diyruz/freepad/Source/OSAL_FreePadApp.c

#include "OSAL.h"
#include "OSAL_Tasks.h"
#include "ZComDef.h"
#include "hal_drivers.h"

#include "APS.h"

#include "ZDApp.h"
#include "nwk.h"

#include "bdb_interface.h"
#ifdef FREEPAD_ENABLE_TL
#include "bdb_touchlink_initiator.h"
#include "stub_aps.h"
#include "tl_resetter.h"
#endif

#include "Debug.h"
#include "battery.h"
#include "commissioning.h"
#include "factory_reset.h"
#include "zcl_freepadapp.h"

const pTaskEventHandlerFn tasksArr[] = {macEventLoop,
                                        nwk_event_loop,
                                        Hal_ProcessEvent,
                                        APS_event_loop,
                                        ZDApp_event_loop,
                                        zcl_event_loop,
#ifdef FREEPAD_ENABLE_TL
                                        StubAPS_ProcessEvent,
                                        touchLinkInitiator_event_loop,
#endif
                                        bdb_event_loop,
                                        zclFreePadApp_event_loop,
                                        zclCommissioning_event_loop,
                                        zclFactoryResetter_loop,
                                        zclBattery_event_loop
#ifdef FREEPAD_ENABLE_TL
                                        ,
                                        zclTouchLinkRestter_event_loop
#endif
};

const uint8 tasksCnt = sizeof(tasksArr) / sizeof(tasksArr[0]);
uint16 *tasksEvents;

void osalInitTasks(void) {
    uint8 taskID = 0;
    DebugInit();

    tasksEvents = (uint16 *)osal_mem_alloc(sizeof(uint16) * tasksCnt);
    osal_memset(tasksEvents, 0, (sizeof(uint16) * tasksCnt));
    macTaskInit(taskID++);
    nwk_init(taskID++);
    Hal_Init(taskID++);
    APS_Init(taskID++);
    ZDApp_Init(taskID++);
    zcl_Init(taskID++);
#ifdef FREEPAD_ENABLE_TL
    StubAPS_Init(taskID++);
    touchLinkInitiator_Init(taskID++);
#endif
    bdb_Init(taskID++);
    zclFreePadApp_Init(taskID++);
    zclCommissioning_Init(taskID++);
    zclFactoryResetter_Init(taskID++);
    zclBattery_Init(taskID++);
#ifdef FREEPAD_ENABLE_TL
    zclTouchLinkRestter_Init(taskID++);
#endif
}

/*********************************************************************
*********************************************************************/
