diyruz/freepad/Source/preinclude.h

#define TC_LINKKEY_JOIN
#define NV_INIT
#define NV_RESTORE
// to make TL work, need patch this macroses in SDK
// #define TOUCHLINK_KEY_INDEX TOUCHLINK_KEY_INDEX_MASTER
// #define TOUCHLINK_INTERNAL_ENDPOINT 42

#define TP2_LEGACY_ZC
// patch sdk
// #define ZDSECMGR_TC_ATTEMPT_DEFAULT_KEY TRUE

#define NWK_AUTO_POLL
#define MULTICAST_ENABLED FALSE

#define ZCL_READ
#define ZCL_WRITE
#define ZCL_BASIC
#define ZCL_IDENTIFY
#define ZCL_ON_OFF
#define ZCL_LEVEL_CTRL
#define ZCL_REPORTING_DEVICE

//TODO: PM3 refactor z2m converters
// #define BDB_REPORTING
// #define FREEPAD_ENABLE_TL
#ifdef FREEPAD_ENABLE_TL
    #define INTER_PAN
    #define BDB_TL_INITIATOR
#endif


#define DISABLE_GREENPOWER_BASIC_PROXY
#define BDB_FINDING_BINDING_CAPABILITY_ENABLED 1


#define ISR_KEYINTERRUPT
#define HAL_BUZZER FALSE

#define HAL_LED TRUE
#define HAL_LCD FALSE
#define BLINK_LEDS TRUE

// one of this boards
// #define HAL_BOARD_FREEPAD
// #define HAL_BOARD_LETV
// #define HAL_BOARD_CHDTECH_DEV

#if !defined(HAL_BOARD_FREEPAD) && !defined(HAL_BOARD_CHDTECH_DEV) && !defined(HAL_BOARD_LETV)
    #error "Board type must be defined"
#endif

#if defined(FREEPAD_ENABLE_TL) && BDB_REPORTING
    #define INT_HEAP_LEN (3000 - 0x38)
#endif

#ifndef INT_HEAP_LEN
    #define INT_HEAP_LEN 3000
#endif

#if defined(HAL_BOARD_LETV)
    #define FREEPAD_BUTTONS_COUNT 8
#else
    #define FREEPAD_BUTTONS_COUNT 20
#endif


#if defined(HAL_BOARD_FREEPAD) || defined(HAL_BOARD_LETV)
    #define POWER_SAVING
#endif

#if defined(HAL_BOARD_CHDTECH_DEV)
    // #define DO_DEBUG_UART
    // #define OSALMEM_METRICS TRUE
#endif

#ifdef DO_DEBUG_UART
    #define HAL_UART TRUE
    #define HAL_UART_DMA 1
    #define INT_HEAP_LEN 2197
#endif

#ifdef DO_DEBUG_MT
    #define HAL_UART TRUE
    #define HAL_UART_DMA 1
    #define HAL_UART_ISR 2
    #define INT_HEAP_LEN (2688-0xC4-0x15-0x44-0x20-0x1E)

    #define MT_TASK

    #define MT_UTIL_FUNC
    #define MT_UART_DEFAULT_BAUDRATE HAL_UART_BR_115200
    #define MT_UART_DEFAULT_OVERFLOW FALSE

    #define ZTOOL_P1

    #define MT_APP_FUNC
    #define MT_APP_CNF_FUNC
    #define MT_SYS_FUNC
    #define MT_ZDO_FUNC
    #define MT_ZDO_MGMT
    #define MT_DEBUG_FUNC
#endif


#include "hal_board_cfg.h"
